AnvitaDey/Autonomous-Underwater-Vehicle-/mechanical-design/hexa-holder/hexa-holder.png

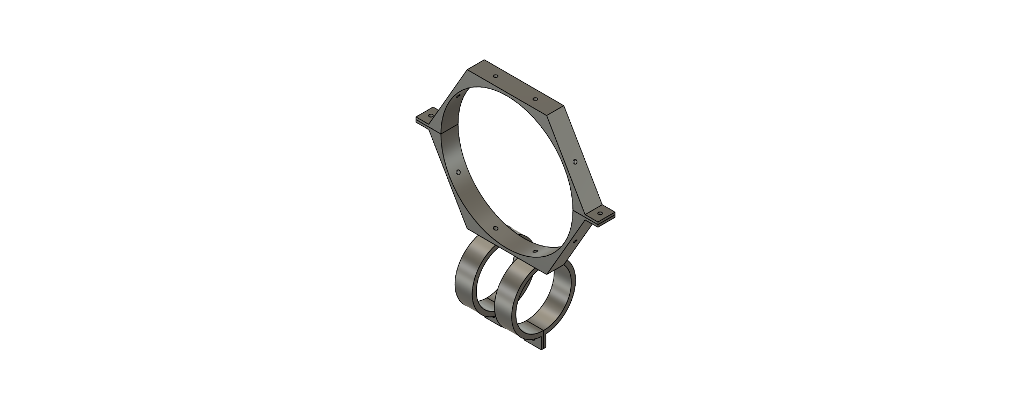
mechanical-design/hexa-holder/hexa-holder.png
