AnvitaDey/Autonomous-Underwater-Vehicle-/system-design/AUV_body_final.png

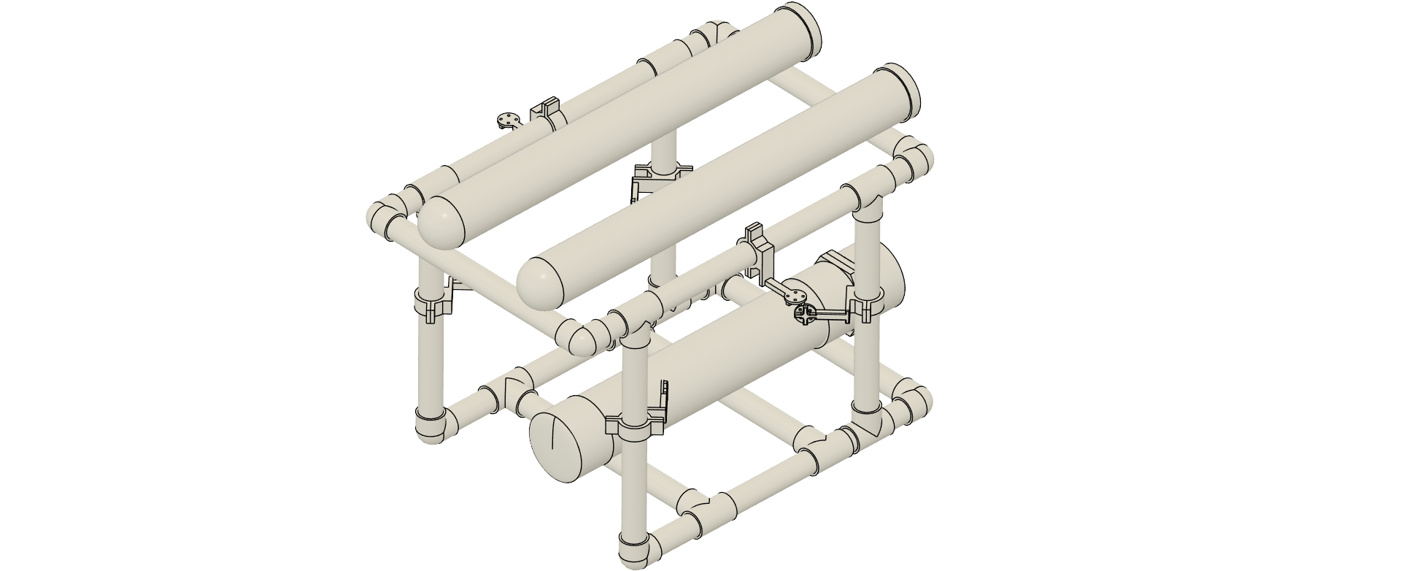
system-design/AUV_body_final.png
